yhsunhelen/TECHIN512_Final-Project/Documentation/FinalProject_Circuit Diagrams.kicad_sch

## KiCad design Documentation/FinalProject_Circuit Diagrams.kicad_sch (2025-12-03)

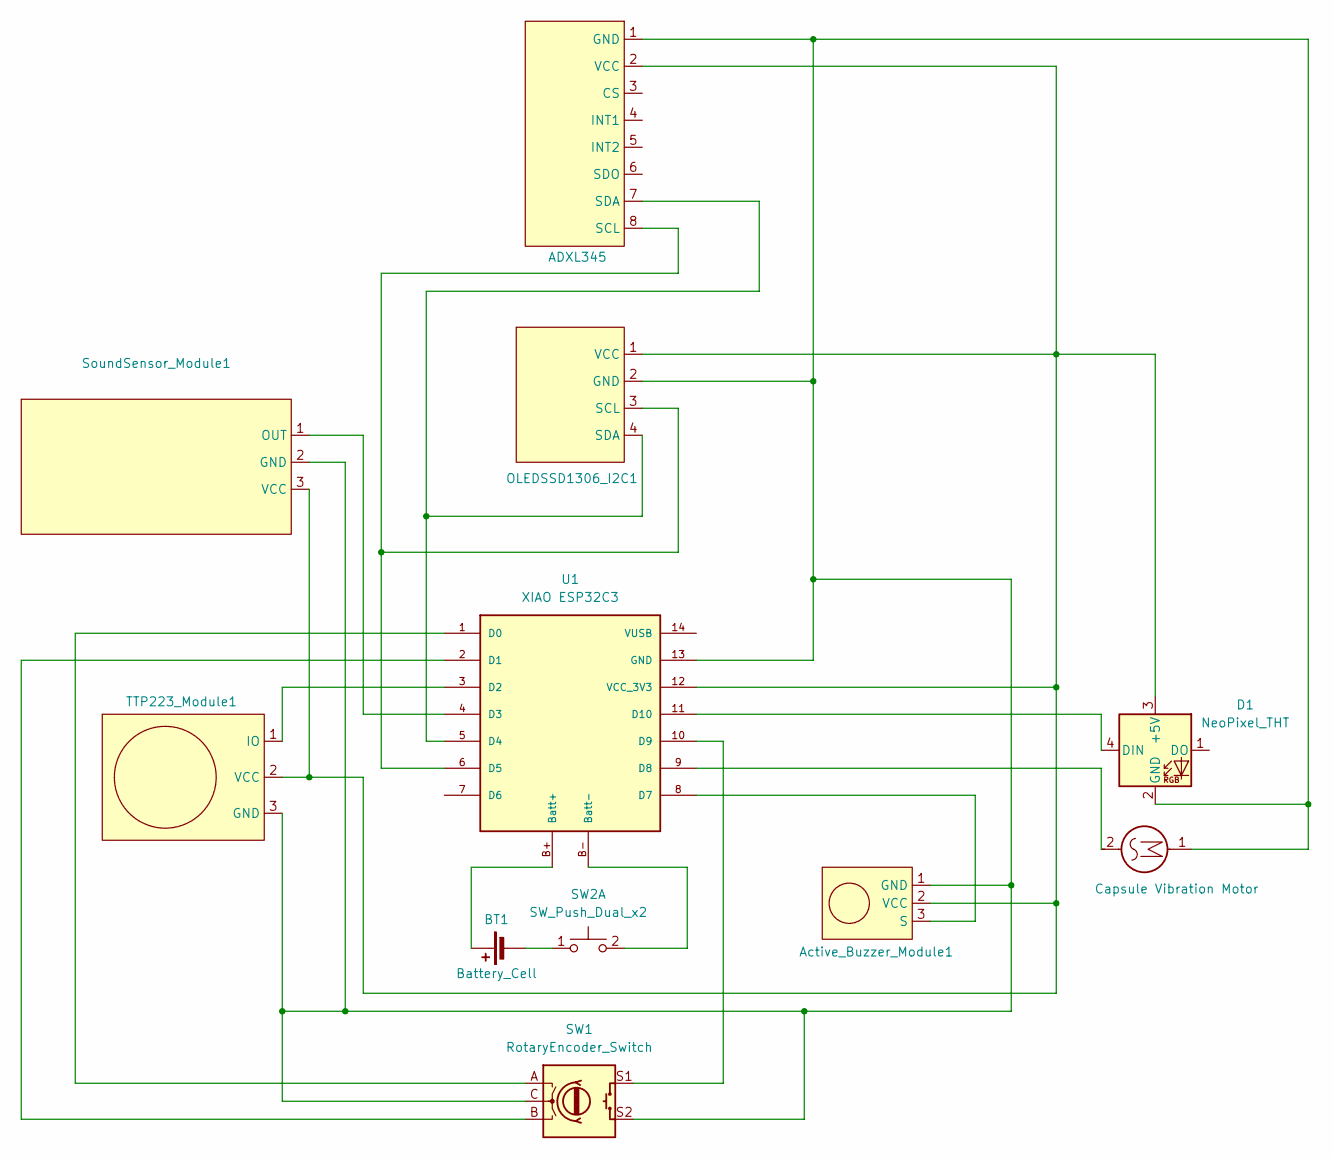
[picture p6: schematic FinalProject_Circuit Diagrams.kicad_sch]

Parts:
ADXL345: (no value)
Active_Buzzer_Module1: (no value)
BT1: Battery_Cell
D1: NeoPixel_THT
M1: Capsule Vibration Motor
OLEDSSD1306_I2C1: (no value)
SW1: RotaryEncoder_Switch
SW2: SW_Push_Dual_x2
SoundSensor_Module1: (no value)
TTP223_Module1: (no value)
U1: XIAO ESP32C3; xiao_esp32c3

Connections:
unnamed: ADXL345.1 (GND), Active_Buzzer_Module1.1 (GND), D1.2 (GND), M1.1, OLEDSSD1306_I2C1.2 (GND), SW1.C, SW1.S2, SoundSensor_Module1.2 (GND), TTP223_Module1.3 (GND), U1.13 (GND)
unnamed: ADXL345.2 (VCC), Active_Buzzer_Module1.2 (VCC), D1.3 (+5V), OLEDSSD1306_I2C1.1 (VCC), SoundSensor_Module1.3 (VCC), TTP223_Module1.2 (VCC), U1.12 (VCC_3V3)
unnamed: ADXL345.7 (SDA), OLEDSSD1306_I2C1.4 (SDA), U1.5 (D4)
unnamed: ADXL345.8 (SCL), OLEDSSD1306_I2C1.3 (SCL), U1.6 (D5)
unnamed: Active_Buzzer_Module1.3 (S), U1.8 (D7)
unnamed: BT1.1 (+), U1.B+ (Batt+)
unnamed: BT1.2 (-), SW2.1 (C)
unnamed: D1.4 (DIN), U1.11 (D10)
unnamed: M1.2, U1.9 (D8)
unnamed: SW1.A, U1.1 (D0)
unnamed: SW1.B, U1.2 (D1)
unnamed: SW1.S1, U1.10 (D9)
unnamed: SW2.2 (D), U1.B- (Batt-)
unnamed: SoundSensor_Module1.1 (OUT), U1.4 (D3)
unnamed: TTP223_Module1.1 (IO), U1.3 (D2)
